jpskenn/Nora/assets/Readme/_DSF1121.jpeg

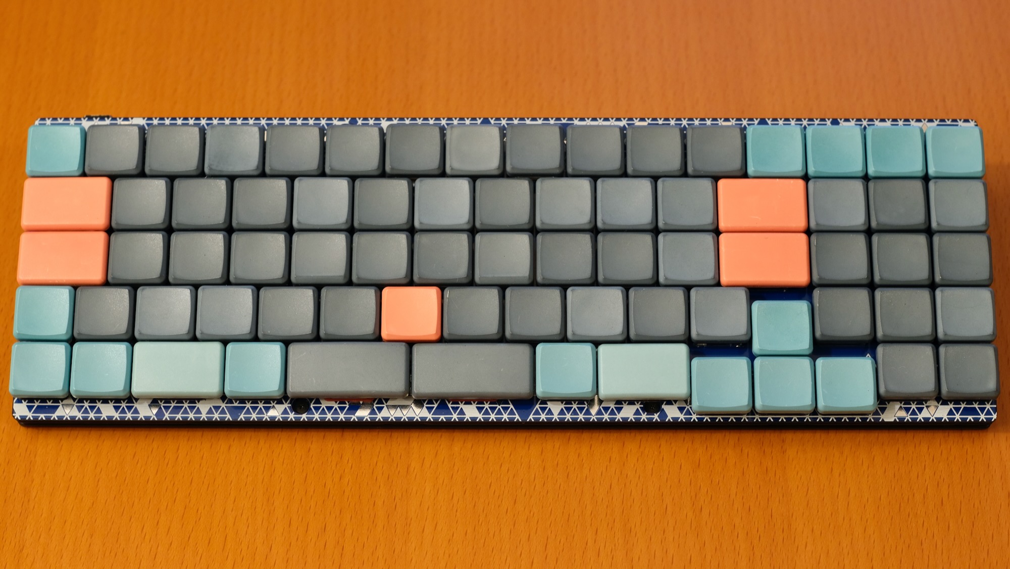
assets/Readme/_DSF1121.jpeg
