jpskenn/Nora/PCB_FW/nora_wide_20211218.jpg

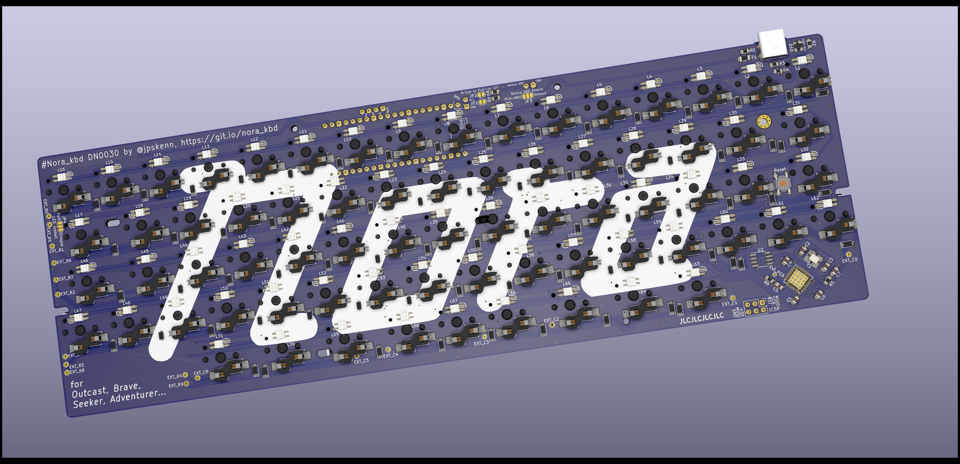
PCB_FW/nora_wide_20211218.jpg
