jpskenn/Nora/Plate_FW/patterns/mask.png

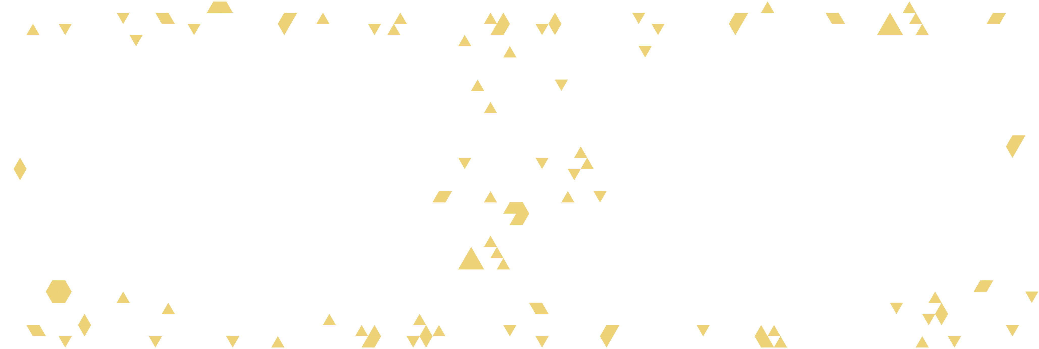
Plate_FW/patterns/mask.png
