jpskenn/Nora/Plate_FW/patterns/mask_full_layout.png

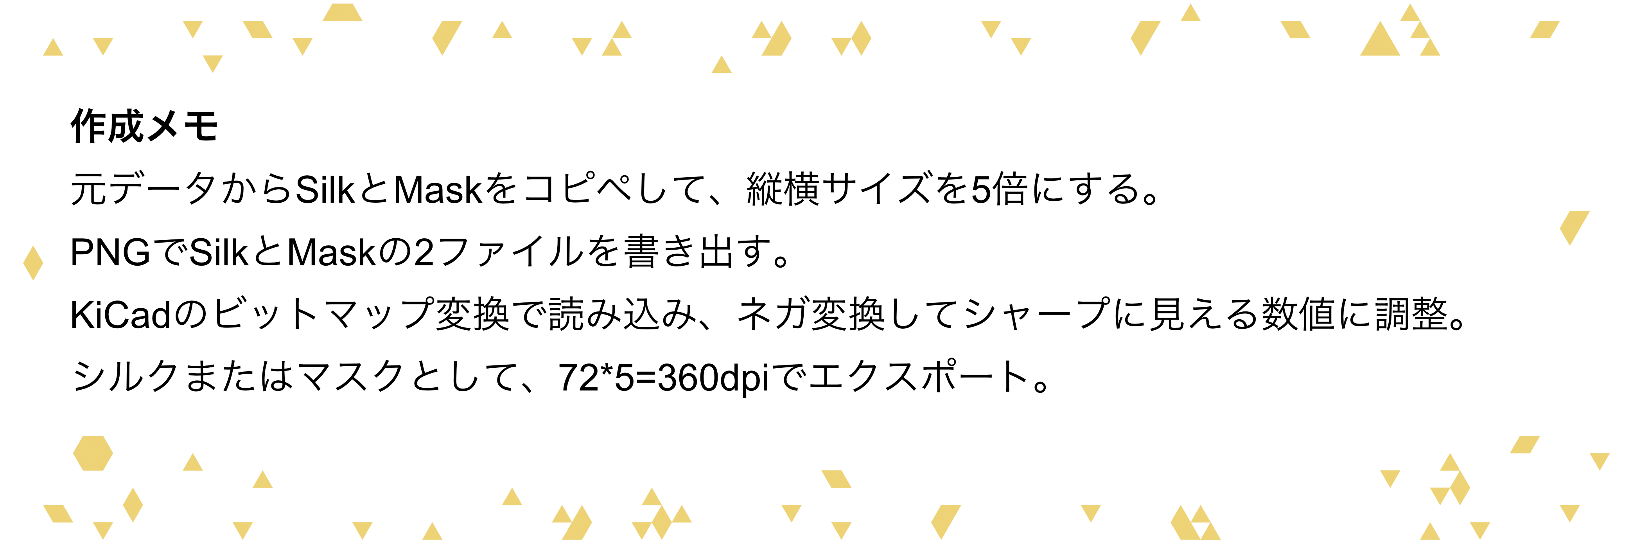
Plate_FW/patterns/mask_full_layout.png
