jpskenn/Nora/Plate_FW/patterns/silk.png

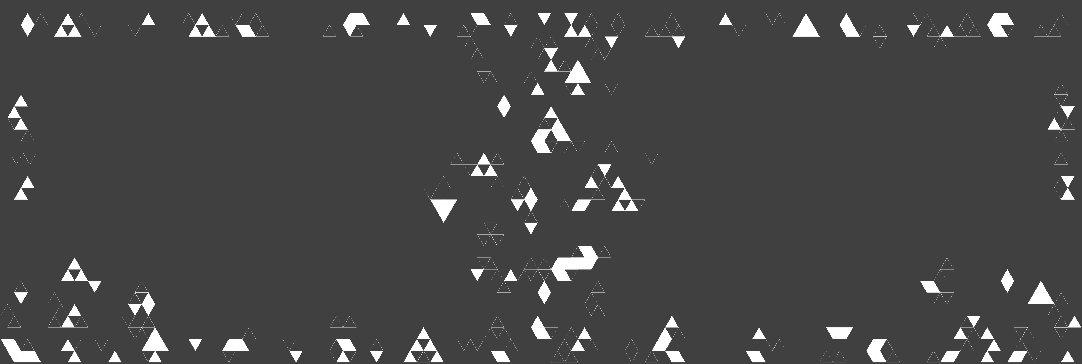
Plate_FW/patterns/silk.png
