jpskenn/Nora/Plate_FW/patterns/silk_full_layout.png

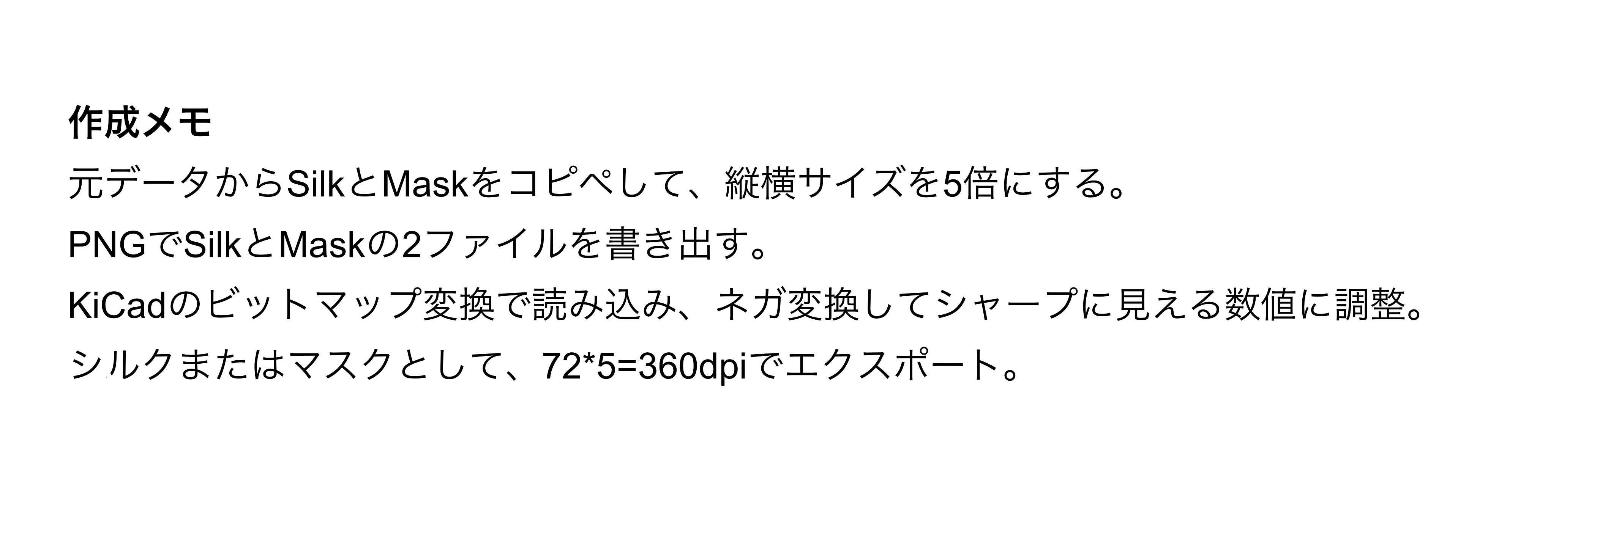
Plate_FW/patterns/silk_full_layout.png
