jpskenn/Nora/assets/BuildGuide_DN0032/Bottom_back.png

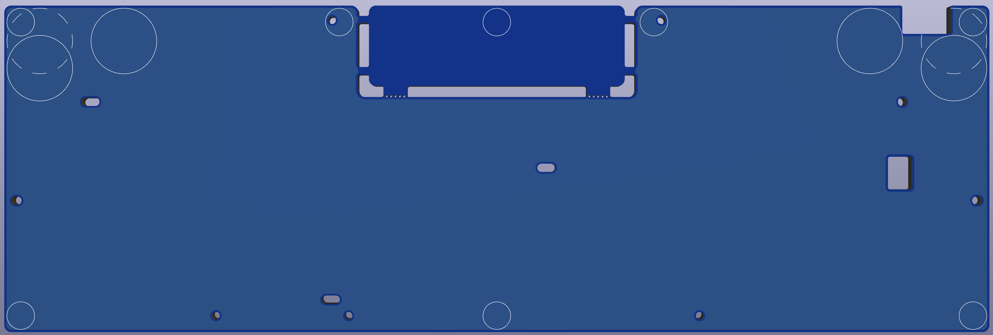
assets/BuildGuide_DN0032/Bottom_back.png
