jpskenn/Nora/assets/BuildGuide_DN0032/DSC_7540.jpeg

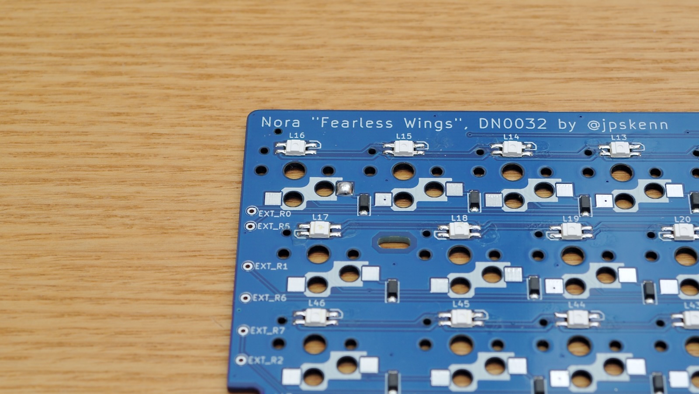
assets/BuildGuide_DN0032/DSC_7540.jpeg
