jpskenn/Nora/assets/BuildGuide_DN0032/DSC_7605.jpeg

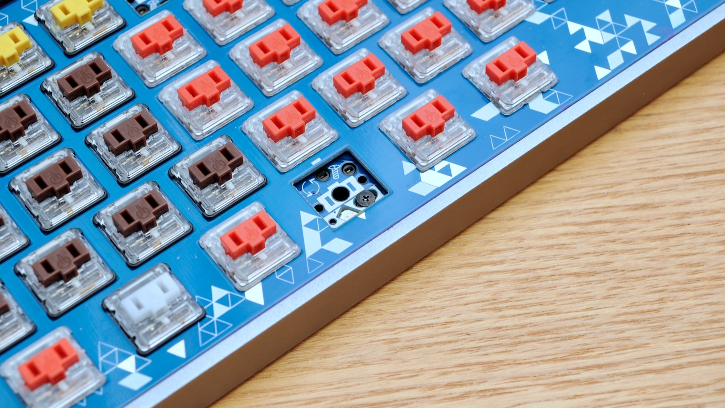
assets/BuildGuide_DN0032/DSC_7605.jpeg
