jpskenn/Nora/assets/BuildGuide_DN0032/PCB_key_pitch.png

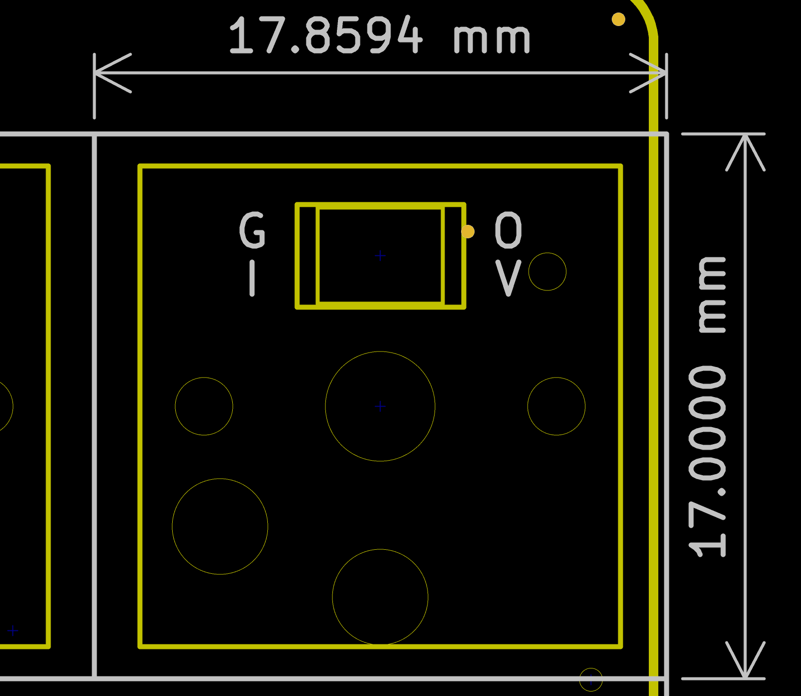
assets/BuildGuide_DN0032/PCB_key_pitch.png
