jpskenn/Nora/assets/BuildGuide_DN0032/QMKToolbox_open.png

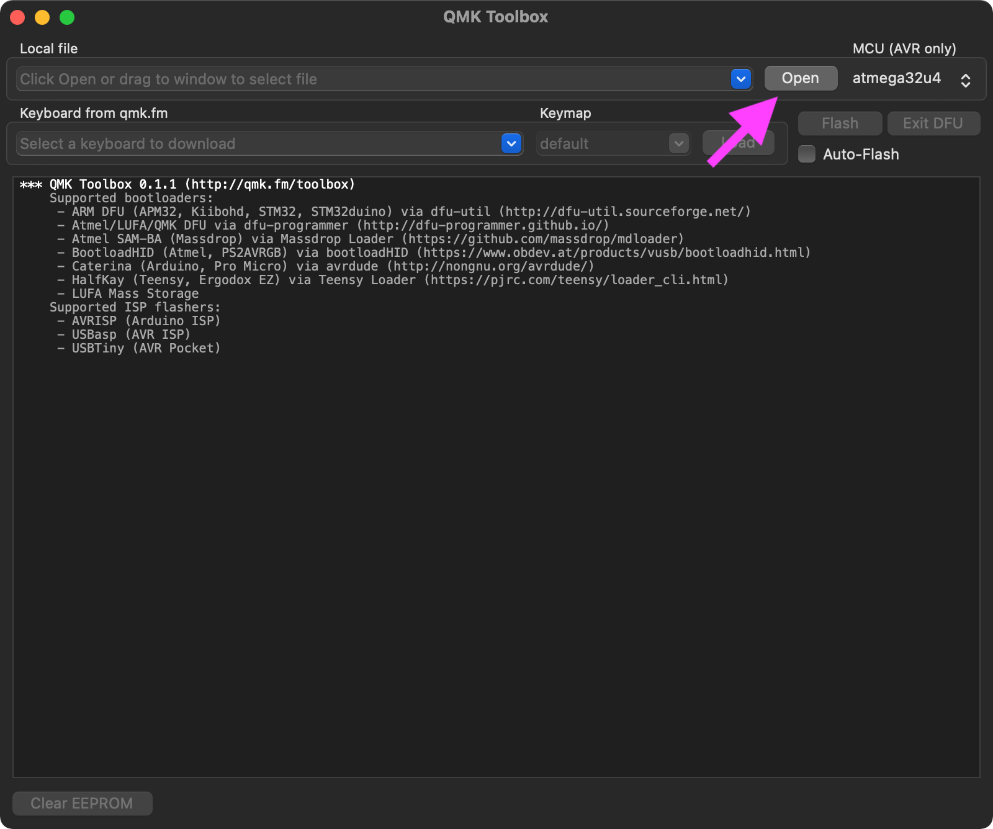
assets/BuildGuide_DN0032/QMKToolbox_open.png
