jpskenn/Nora/assets/BuildGuide_DN0032/Remap_catalog_nora_v1.png

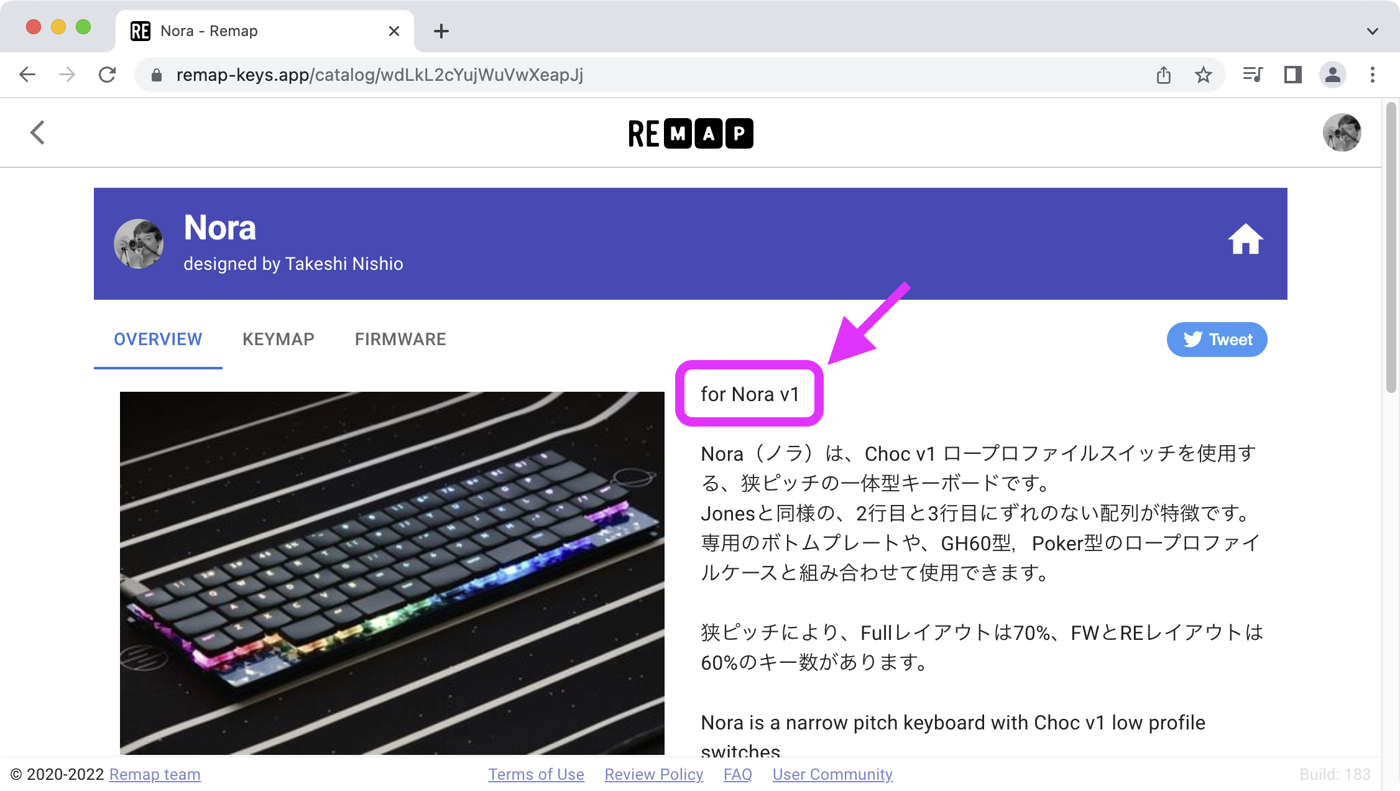
assets/BuildGuide_DN0032/Remap_catalog_nora_v1.png
